blinken/paradar/doc/978MHz-1200.png

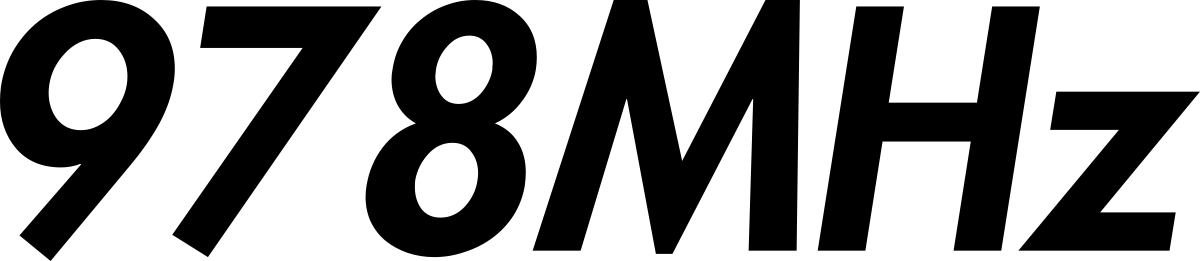
doc/978MHz-1200.png
