blinken/paradar/doc/1090MHz-1200.png

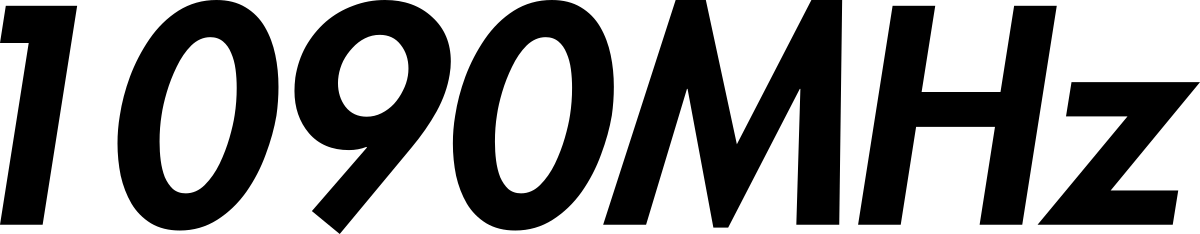
doc/1090MHz-1200.png
