blinken/paradar/doc/images/20200324-blue-case-800.png

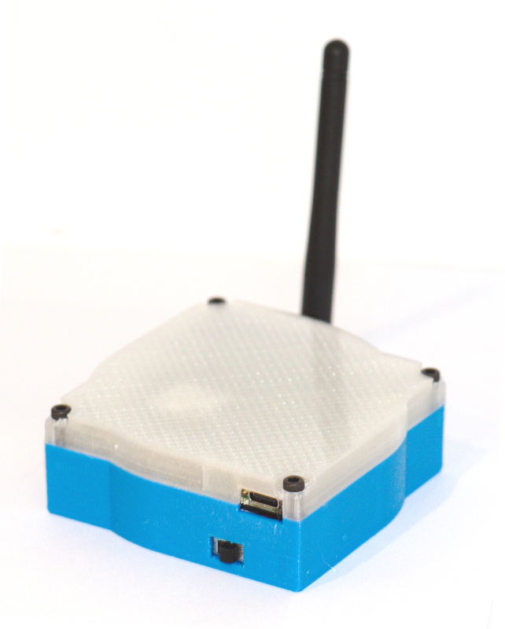
doc/images/20200324-blue-case-800.png
