blinken/paradar/doc/images/v1.4/DSC_7962-800.png

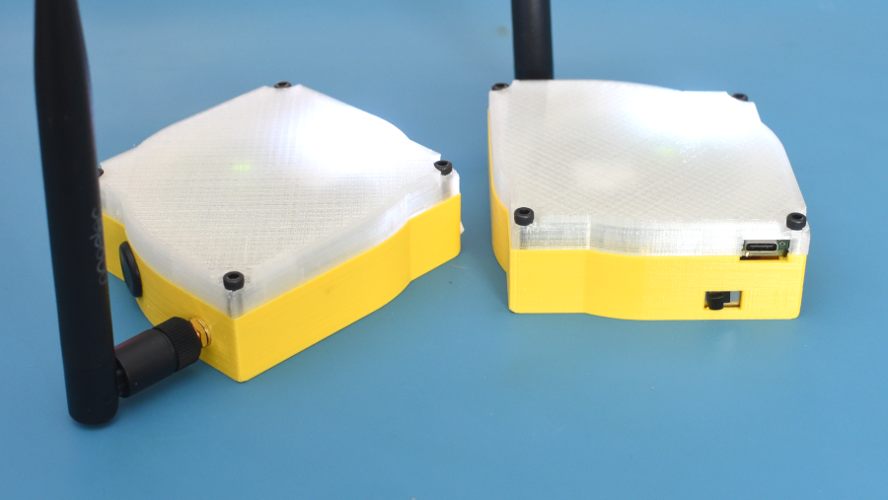
doc/images/v1.4/DSC_7962-800.png
