blinken/paradar/doc/images/v1.4/DSC_7970-800.png

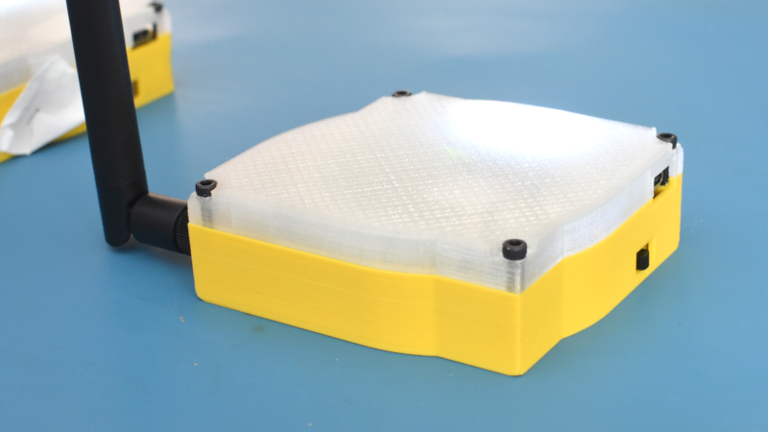
doc/images/v1.4/DSC_7970-800.png
