blinken/paradar/doc/images/v1.4/DSC_7973-1200.png

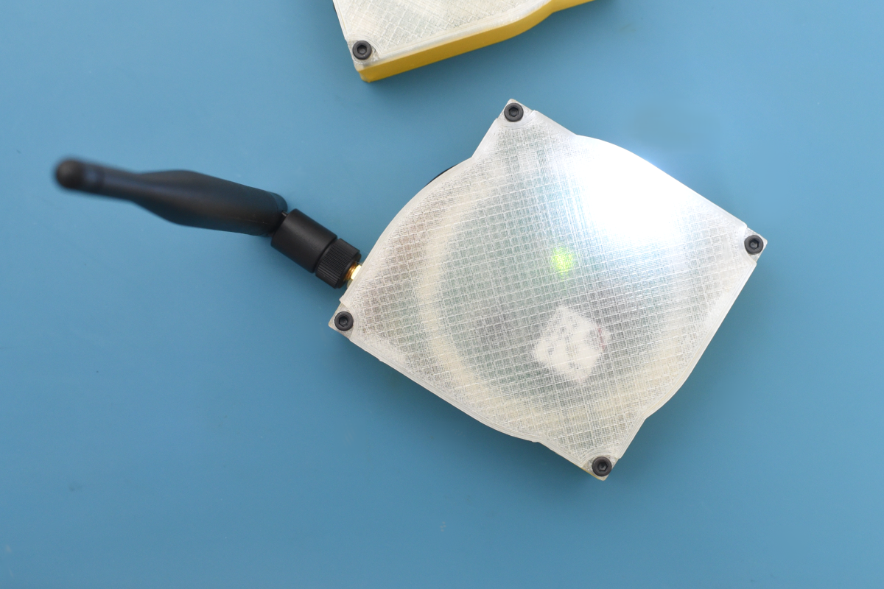
doc/images/v1.4/DSC_7973-1200.png
