blinken/paradar/doc/images/v1.4/DSC_7979-1200.png

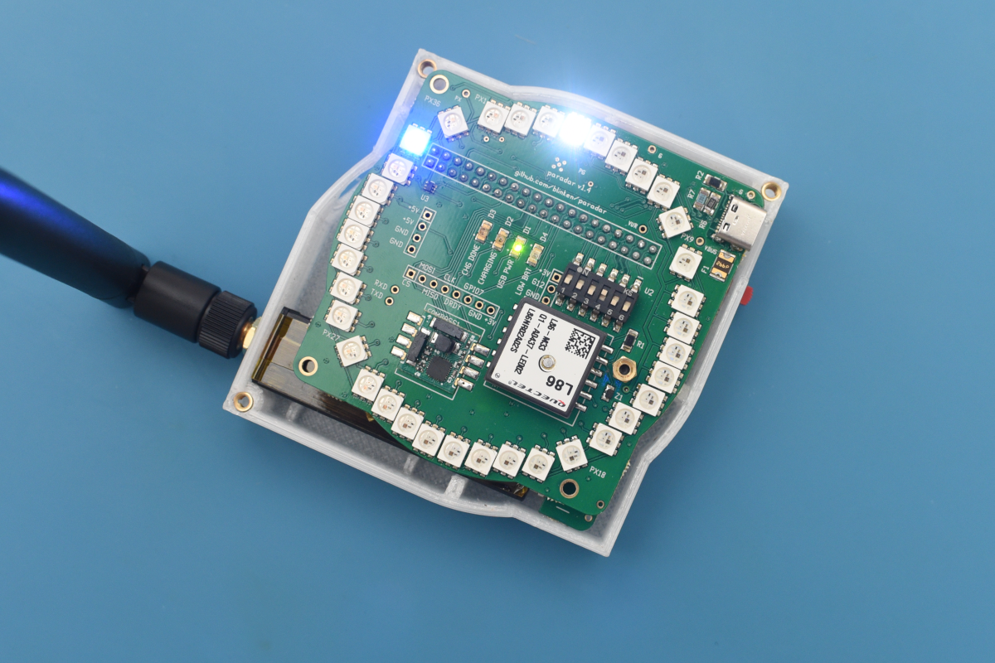
doc/images/v1.4/DSC_7979-1200.png
