blinken/paradar/pcb/pizero-usb-rightangle/v1.2b-panelised/bottom.png

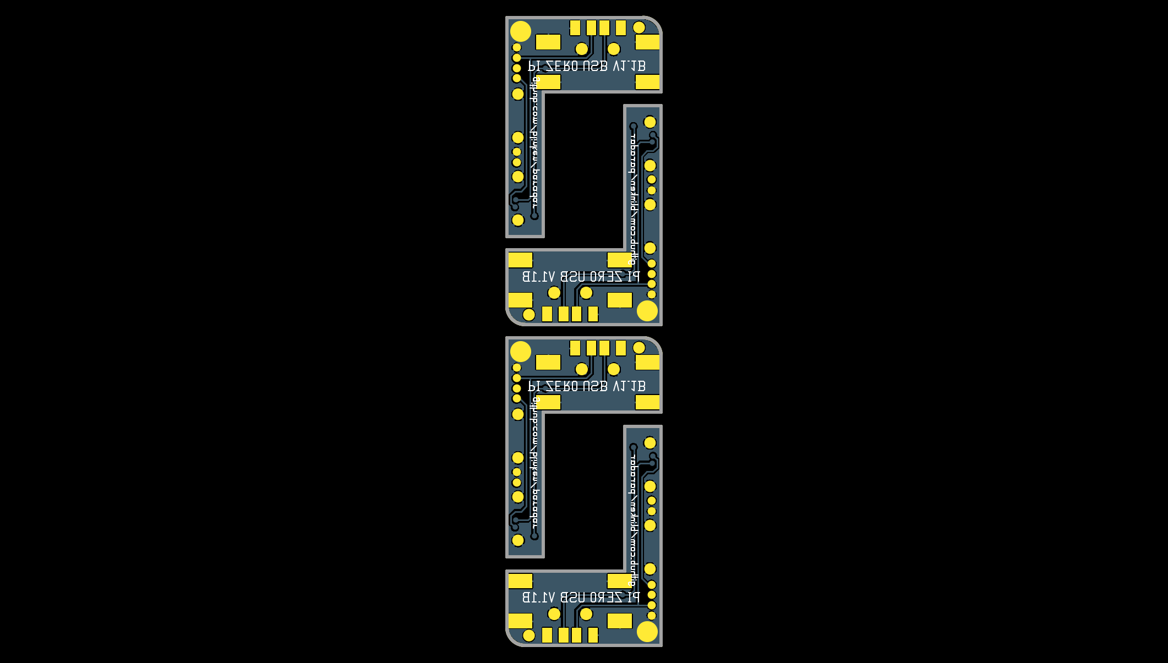
pcb/pizero-usb-rightangle/v1.2b-panelised/bottom.png
