blinken/paradar/pcb/pizero-usb-rightangle/v1.2b-panelised/v1_Combined_Top.png

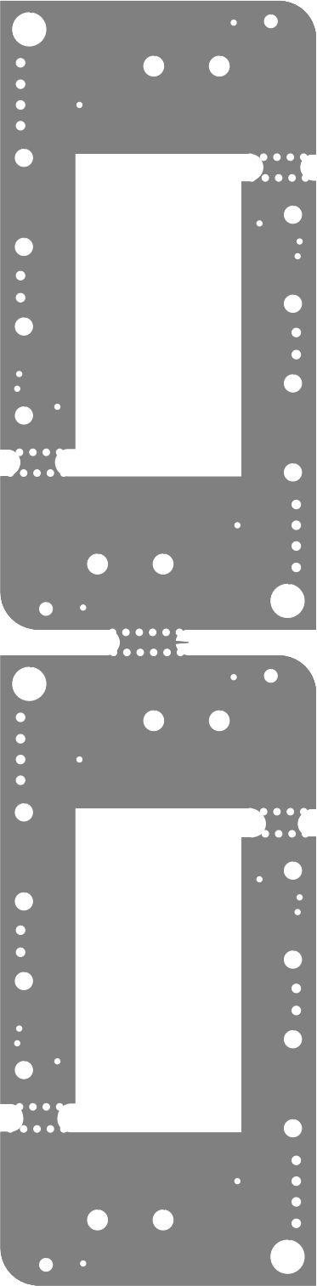
pcb/pizero-usb-rightangle/v1.2b-panelised/v1_Combined_Top.png
